FredericSegard/Fr80/2 - CPU and core components (Rev 3)/BAK/2 - CPU and core components (Rev 3).jpg

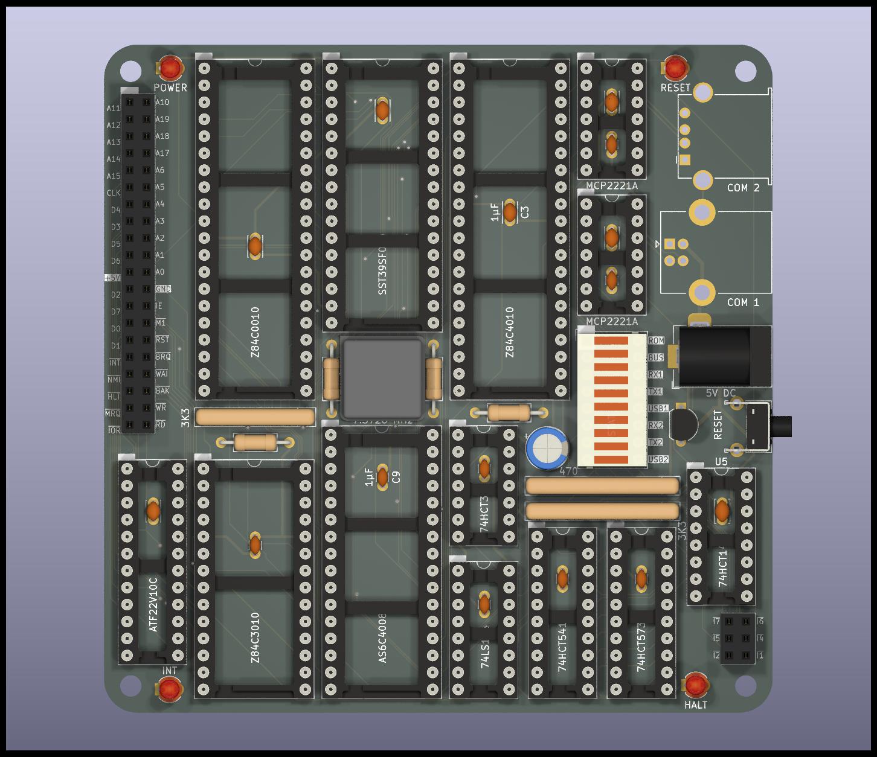
2 - CPU and core components (Rev 3)/BAK/2 - CPU and core components (Rev 3).jpg
