FredericSegard/Fr80/2 - CPU and core components (Rev 3)/Docs and Images/Side view.jpg

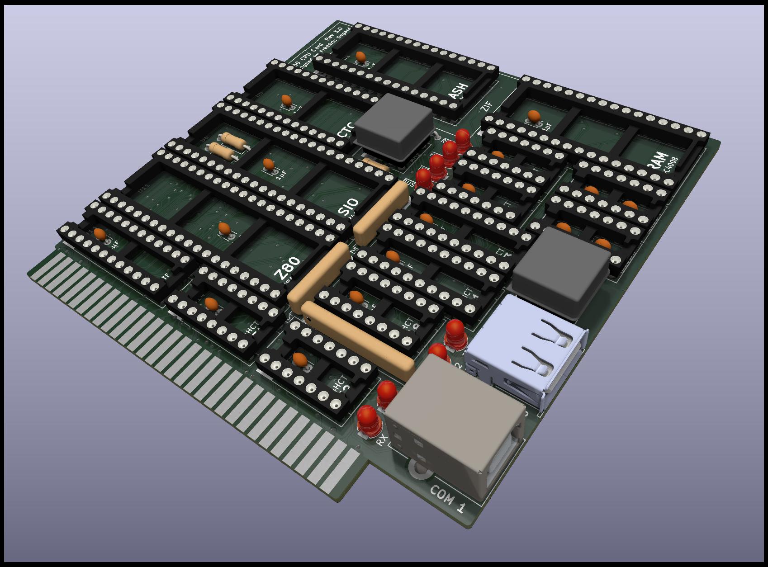
2 - CPU and core components (Rev 3)/Docs and Images/Side view.jpg
